SassyDice/Wireless-Turret-Gun/#Taret Projesi/3D Tasarım/littlefrenchkev's stl parts/genel parçalar/Bluetooth_bracket.stl

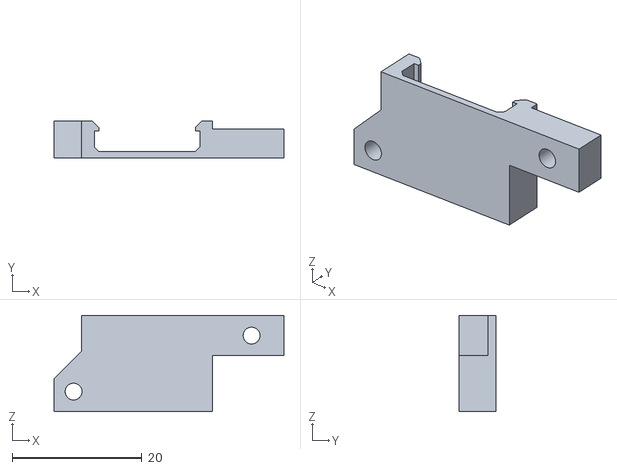
[picture p43: CAD file, 2021-06-02]
#Taret Projesi/3D Tasarım/littlefrenchkev's stl parts/genel parçalar/Bluetooth_bracket.stl
35.5 x 5.65 x 14.8
