SassyDice/Wireless-Turret-Gun/#Taret Projesi/3D Tasarım/littlefrenchkev's stl parts/genel parçalar/Tilt_bracket_bottom.stl

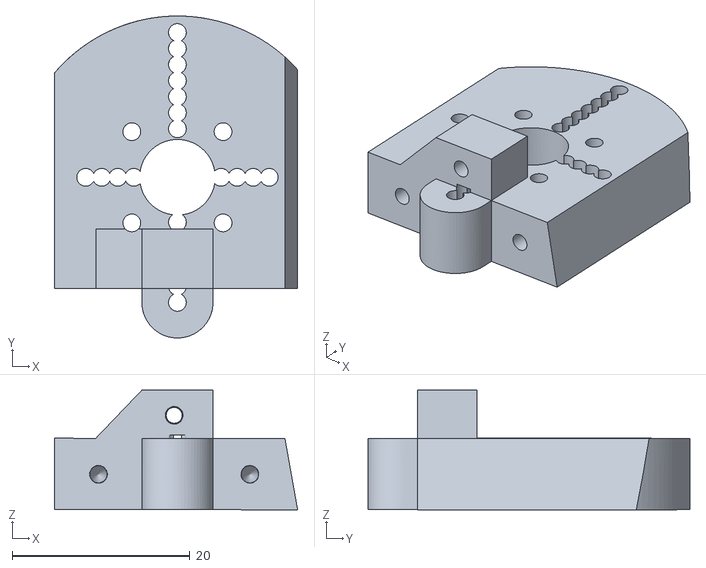
[picture p44: CAD file, 2021-06-02]
#Taret Projesi/3D Tasarım/littlefrenchkev's stl parts/genel parçalar/Tilt_bracket_bottom.stl
27.3 x 36.2 x 13.5
